anirudh12032008/deskorganizer/modular desk/Plate10_container_base.step

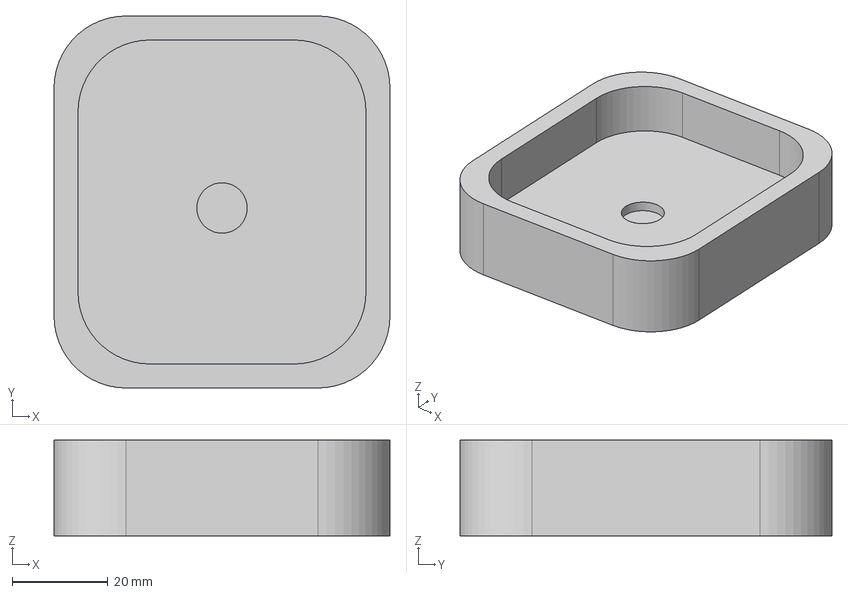
[picture p15: CAD file, 2025-12-29]
modular desk/Plate10_container_base.step
70.0 x 77.5 x 20.0 mm
