anirudh12032008/deskorganizer/modular desk/Plate10_container_upper.step

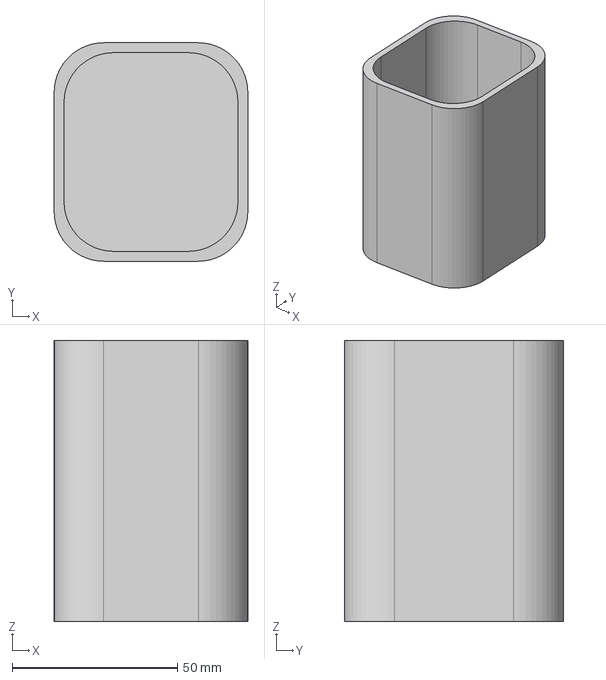
[picture p16: CAD file, 2025-12-29]
modular desk/Plate10_container_upper.step
58.6 x 66.1 x 85.0 mm
