anirudh12032008/deskorganizer/modular desk/Plate10_tray.step

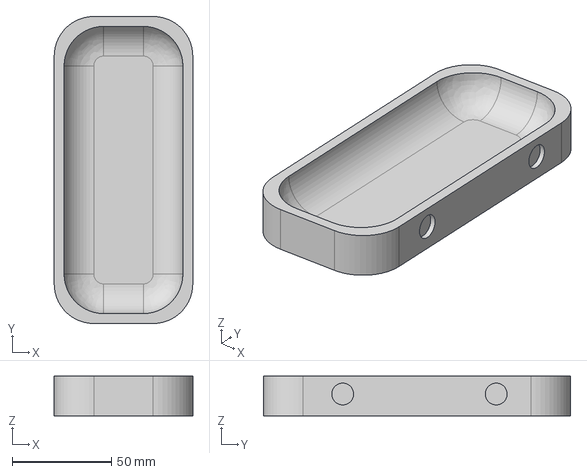
[picture p17: CAD file, 2025-12-29]
modular desk/Plate10_tray.step
70.0 x 155.0 x 20.0 mm
